Queens-Rocket-Engineering-Team/av-prop-integration/Schematics/lower_lc_board/models/m20-8890445r.stp

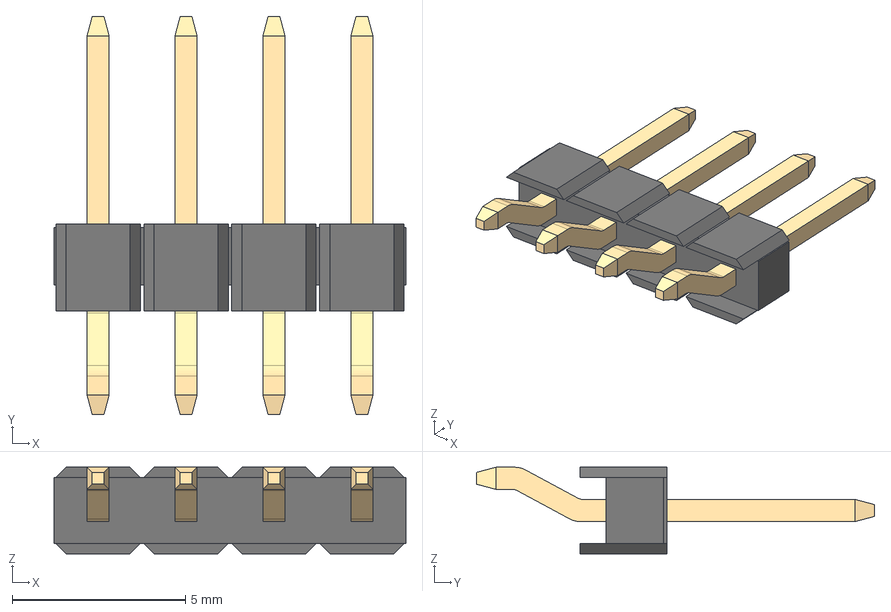
[picture p16: CAD file, 2026-03-23]
Schematics/lower_lc_board/models/m20-8890445r.stp
10.2 x 11.5 x 2.50 mm
