Queens-Rocket-Engineering-Team/av-prop-integration/Schematics/shared_schematics/models/1053131102.step

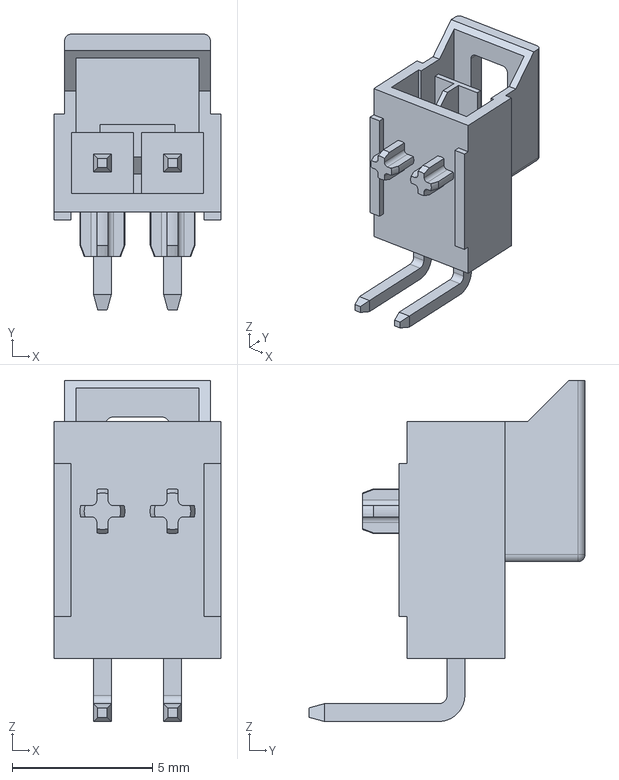
[picture p17: CAD file, 2026-03-23]
Schematics/shared_schematics/models/1053131102.step
5.94 x 9.84 x 12.2 mm
