Queens-Rocket-Engineering-Team/av-prop-integration/Schematics/shared_schematics/models/1053091102.step

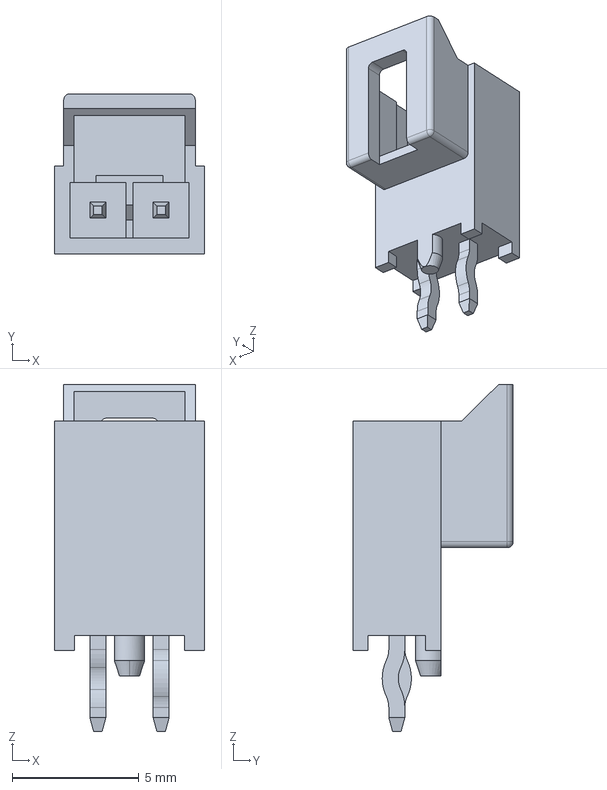
[picture p18: CAD file, 2026-03-23]
Schematics/shared_schematics/models/1053091102.step
5.94 x 6.34 x 13.7 mm
