Queens-Rocket-Engineering-Team/av-prop-integration/Schematics/lower_lc_board/models/430450602.stp

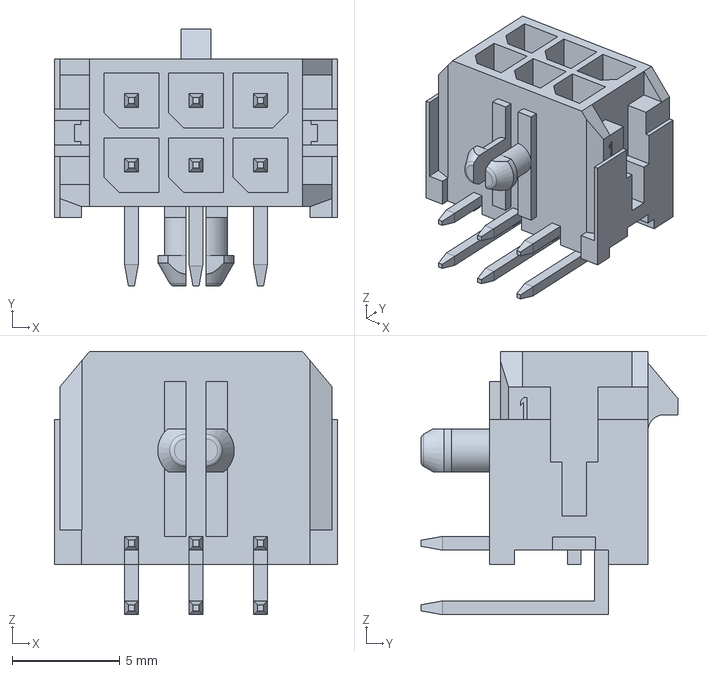
[picture p19: CAD file, 2026-03-23]
Schematics/lower_lc_board/models/430450602.stp
13.2 x 11.9 x 12.2 mm
